DanielRossi1/ToF-Thermal-Cam-Array/sensor_array_idf/main/hub_control.h

#pragma once

#include <stddef.h>
#include <stdint.h>

#include "hub_protocol.h"
#include "hub_transport.h"

#include "camera_sync.h"
#include "i2c_bus.h"
#include "mlx90640_driver.h"
#include "tof_vl53l8ch.h"

#if HUB_USE_UVC_CAMERA
#include "uvc_camera.h"
#endif

namespace hub {

struct ControlContext {
  Transport*      tx          = nullptr;
  I2CBus*         i2c         = nullptr;
  TofVl53l8ch*    tof         = nullptr;
  Mlx90640Driver* mlx         = nullptr;
  CameraSync*     cam_sync    = nullptr;

#if HUB_USE_UVC_CAMERA
  UvcCamera*      cam         = nullptr;
  bool*           cam_started = nullptr;
#endif

  volatile bool*  stream_enabled = nullptr;
};

void handleSlipFrame(const uint8_t* data, size_t len, void* user);

}  // namespace hub
