DanielRossi1/ToF-Thermal-Cam-Array/sensor_array_idf/components/Adafruit_MLX90640/mlx90640_idf_hal.h

#pragma once
#include "driver/i2c.h"

#ifdef __cplusplus
extern "C" {
#endif

// Call once before using any MLX90640 driver functions.
void MLX90640_IDF_SetPort(i2c_port_t port);

#ifdef __cplusplus
}
#endif
